gabotrix/mesero-ai/docs/img/case-exploded.png

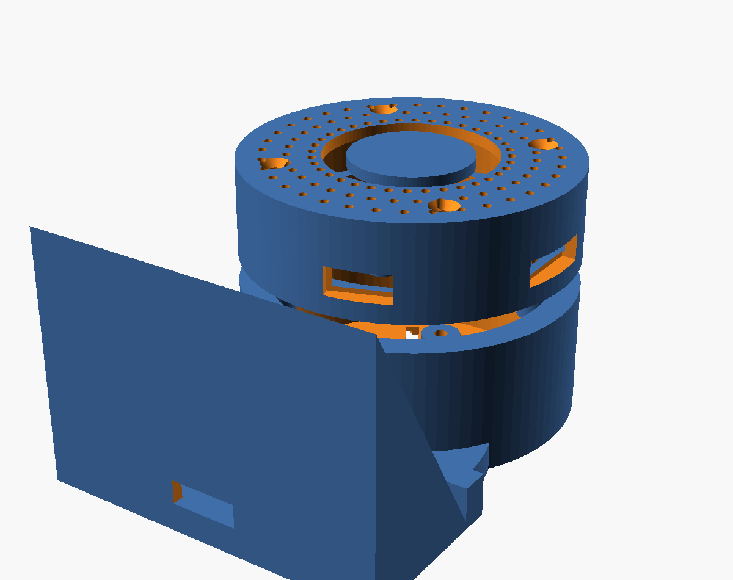
docs/img/case-exploded.png
