gabotrix/mesero-ai/docs/img/case-side.png

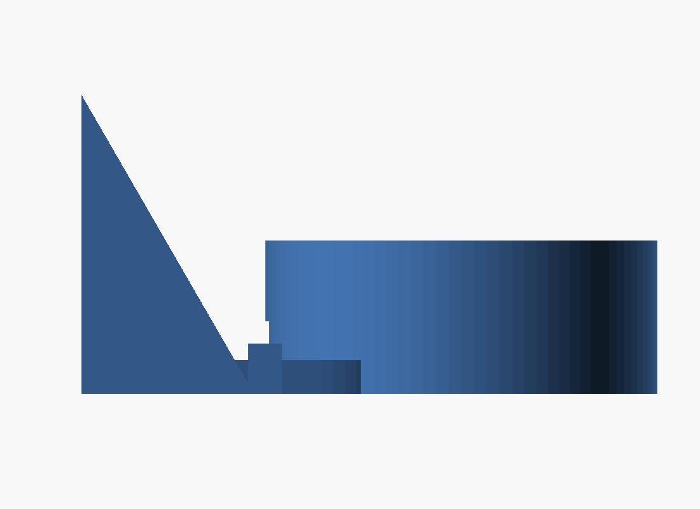
docs/img/case-side.png
