gabotrix/mesero-ai/hardware/case/m-check.png

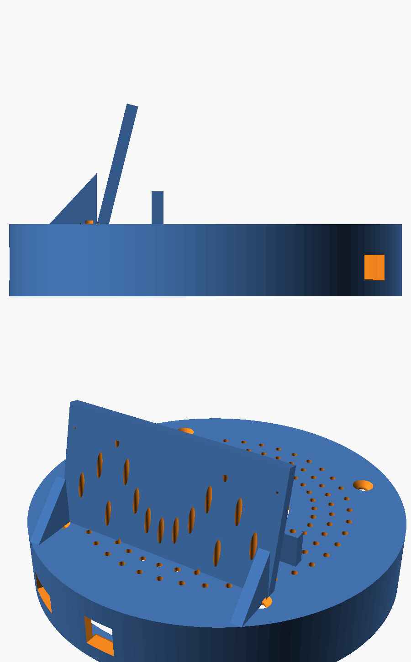
hardware/case/m-check.png
