gabotrix/mesero-ai/hardware/schematics/mesero-ai-pines.png

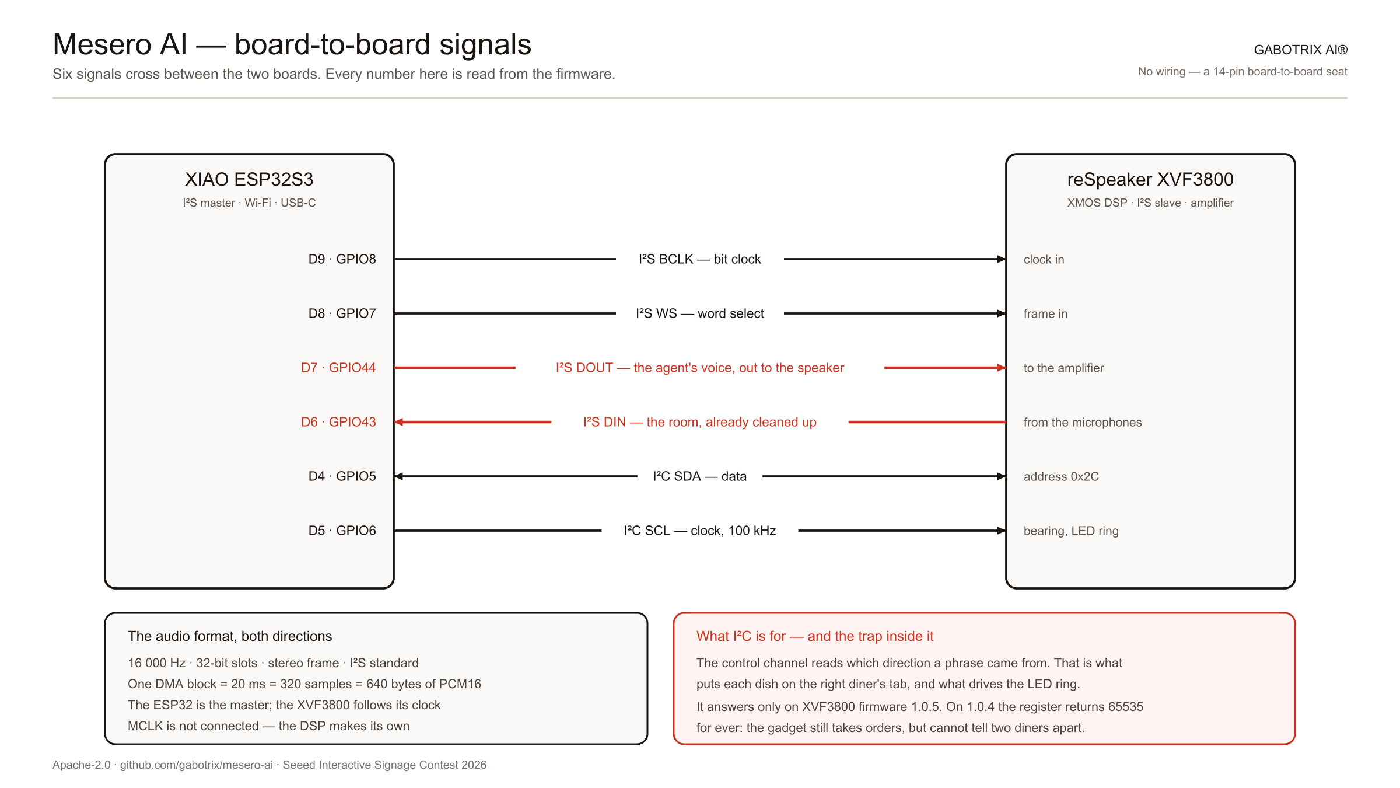
hardware/schematics/mesero-ai-pines.png
