gabotrix/mesero-ai/firmware/src/portal_ui.h

#pragma once
#include <Arduino.h>

/**
 * The setup portal's skin.
 *
 * The first thing anybody sees of this project is not the table screen — it is
 * this page, on a phone, standing next to a device that does not work yet.
 * WiFiManager's default reads like a router admin page and gives no signal that
 * the thing in your hand is finished.
 *
 * The branding is pure CSS on purpose. An earlier version built the header with
 * a script, which meant that anywhere the script did not run — a saved copy, a
 * restricted captive-portal browser, a snapshot — the page lost its logo and
 * looked broken. A background-image on body::before always renders.
 *
 * The logo is the real mark, downscaled to 400 px and stripped to white plus
 * alpha, which is all the information a flat silhouette carries. 11 KB of
 * base64, served from the device itself: the portal runs on an access point with
 * no internet behind it, so nothing here can be fetched.
 *
 * On the QR: the venue key can arrive as ?venue= in the URL, which is what the
 * console encodes. It cannot be scanned *by this page* — getUserMedia needs a
 * secure context and a captive portal is plain HTTP at 192.168.4.1, so no
 * browser will open a camera here. The phone's own camera app scans it, opens
 * this URL, and the field fills itself.
 */

static const char PORTAL_HEAD[] PROGMEM = R"HEAD(
<meta name="viewport" content="width=device-width,initial-scale=1,viewport-fit=cover">
<meta name="theme-color" content="#0b4ea2">
<style>
:root{
  --brand:#1a73e8; --deep:#072f63; --mid:#0b4ea2;
  --ink:#0e1c2b; --muted:#61707f; --line:#e2e8f0; --field:#f7f9fc;
}
*{box-sizing:border-box}
body{
  margin:0; padding:0 0 44px; min-height:100vh;
  background:#eef2f7; color:var(--ink);
  font-family:'Montserrat',-apple-system,BlinkMacSystemFont,'Segoe UI',Roboto,sans-serif;
  -webkit-font-smoothing:antialiased; font-size:15px;
}

/* Header, logo and all, without a line of script. */
body:before{
  content:"Configura esta mesa";
  display:block; padding:84px 20px 26px;
  background:
    url("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") no-repeat center 30px / 188px auto,
    radial-gradient(ellipse 70% 130% at 15% 0%,rgba(77,151,245,.55),transparent 65%),
    linear-gradient(150deg,var(--deep),var(--mid) 55%,var(--brand));
  color:#cfe0f7; text-align:center;
  font-size:12.5px; font-weight:600; letter-spacing:.09em; text-transform:uppercase;
}

.wrap{
  width:min(100%,440px); margin:-16px auto 0; position:relative;
  padding:22px 20px 24px; background:#fff;
  border:1px solid var(--line); border-radius:18px;
  box-shadow:0 14px 34px rgba(7,47,99,.13); text-align:left;
}
@media(max-width:480px){ .wrap{margin:-16px 12px 0} }

h1{margin:0 0 18px; font-size:21px; font-weight:800; letter-spacing:-.02em}
h3{margin:0 0 12px; font-size:14px; font-weight:800; color:var(--muted)}

label,dt{display:block; margin-bottom:5px; font-size:12px; font-weight:800; letter-spacing:.02em}
input,select{
  width:100%; padding:13px 14px; margin:0 0 15px;
  font:inherit; font-size:16px;      /* under 16px and iOS zooms on focus */
  font-weight:600; color:var(--ink); background:var(--field);
  border:1px solid var(--line); border-radius:11px;
}
input:focus,select:focus{
  outline:none; background:#fff; border-color:var(--brand);
  box-shadow:0 0 0 3px rgba(26,115,232,.18);
}
input::placeholder{font-weight:500; color:#9aa8b6}

button,input[type=submit]{
  width:100%; min-height:52px; margin:6px 0 4px; padding:0 18px;
  font:inherit; font-size:15px; font-weight:800; letter-spacing:.01em;
  color:#fff; cursor:pointer; border:0; border-radius:13px;
  background:linear-gradient(135deg,var(--mid),var(--brand));
  box-shadow:0 8px 20px rgba(26,115,232,.30);
}
button:active{transform:translateY(1px)}
a{color:var(--brand); font-weight:700; text-decoration:none}

.msg{
  padding:13px 15px; margin:0 0 18px; font-size:13px; line-height:1.55;
  color:#0b3c78; background:#eaf2fd; border:1px solid #cfe0f7;
  border-radius:12px;
}
.q{float:right; color:var(--muted); font-size:11.5px; font-weight:700}

/* Folded away, not removed: most people never open it, and somebody running
   their own backend must still be able to find it. */
.gbx-adv{margin:4px 0 16px; border-top:1px solid var(--line); padding-top:12px}
.gbx-adv summary{
  cursor:pointer; list-style:none;
  font-size:12.5px; font-weight:800; color:var(--muted);
}
.gbx-adv summary::-webkit-details-marker{display:none}
.gbx-adv summary:before{content:"+ "; font-weight:800}
.gbx-adv[open] summary:before{content:"- "}
.gbx-adv-note{margin:10px 0 14px; font-size:11.5px; line-height:1.55; color:var(--muted)}
.gbx-hint{margin:-10px 0 16px; font-size:11.5px; line-height:1.5; color:var(--muted)}
.gbx-ok{color:#0f7b46; font-weight:700}
</style>
<script>
// Everything the gadget needs can ride in on the URL — that is what the QR the
// console prints for each table encodes. Held in sessionStorage because
// WiFiManager walks across more than one page and the query string does not
// survive the trip.
//
// It is one QR per table, not one per restaurant: the dock is what pairs this
// gadget with the diner's phone, and it differs at every table.
document.addEventListener('DOMContentLoaded',function(){
  var FIELDS=['venue','dock','host','port'];
  try{
    var q=new URLSearchParams(location.search), got=false;
    FIELDS.forEach(function(k){
      var v=q.get(k);
      if(v){ sessionStorage.setItem('gbx_'+k,v); }
    });
    FIELDS.forEach(function(k){
      var v=sessionStorage.getItem('gbx_'+k);
      var f=document.getElementById(k);
      // The QR wins over what is on the device. It has to: the table id always
      // starts at its compiled default, so refusing to overwrite left every
      // table after the first one silently calling itself mesa-01. The person
      // sees what it filled in and confirms before saving — that is the check.
      if(f&&v){ f.value=v; got=true; }
    });
    var anchor=document.getElementById('venue');
    if(got&&anchor){
      var h=document.createElement('p');
      h.className='gbx-hint';
      h.innerHTML='<span class="gbx-ok">Datos recibidos del codigo QR.</span> '
        +'Revisalos y elige tu red WiFi; se guardan al terminar.';
      anchor.parentNode.insertBefore(h,anchor.nextSibling);
    }
  }catch(e){}
});
</script>
)HEAD";
